sini6a/bratski-keyboard/keycaps/1x2.75 R2.stl

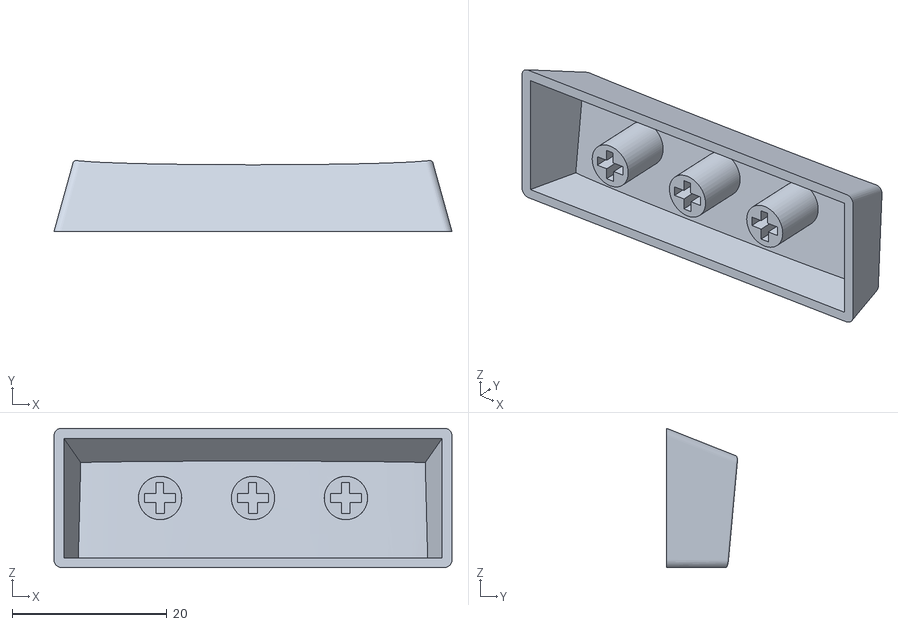
[picture p21: CAD file, 2024-02-13]
keycaps/1x2.75 R2.stl
51.4 x 9.14 x 18.0
