sini6a/bratski-keyboard/keycaps/1x2 R1.stl

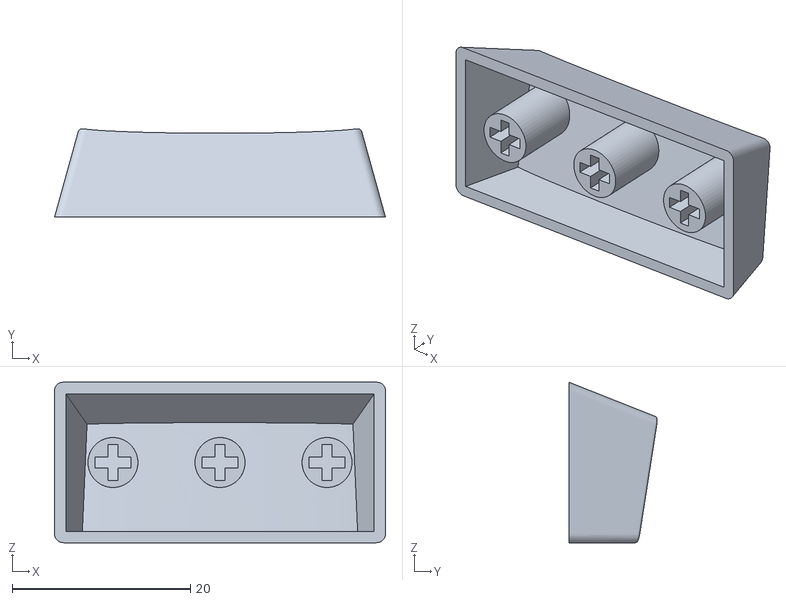
[picture p22: CAD file, 2024-02-13]
keycaps/1x2 R1.stl
37.1 x 9.88 x 18.0
