sini6a/bratski-keyboard/keycaps/1x1.25 R3.stl

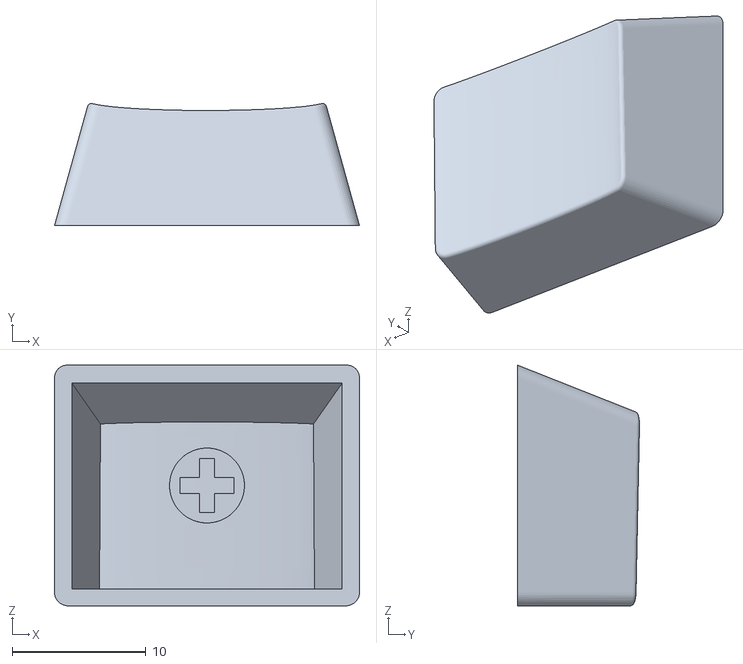
[picture p23: CAD file, 2024-02-13]
keycaps/1x1.25 R3.stl
22.8 x 9.12 x 18.0
