sini6a/bratski-keyboard/keycaps/1x6.25 R3.stl

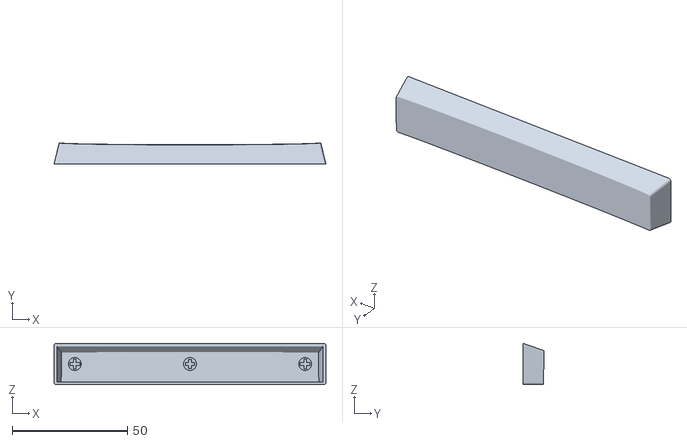
[picture p24: CAD file, 2024-02-13]
keycaps/1x6.25 R3.stl
118.1 x 9.20 x 18.0
