sini6a/bratski-keyboard/keycaps/1x1.5 R1.stl

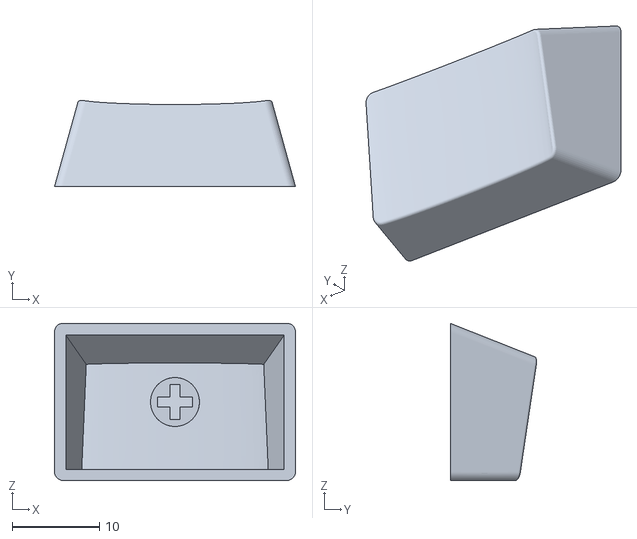
[picture p25: CAD file, 2024-02-13]
keycaps/1x1.5 R1.stl
27.6 x 9.86 x 18.0
