sini6a/bratski-keyboard/keycaps/1x1 R1.stl

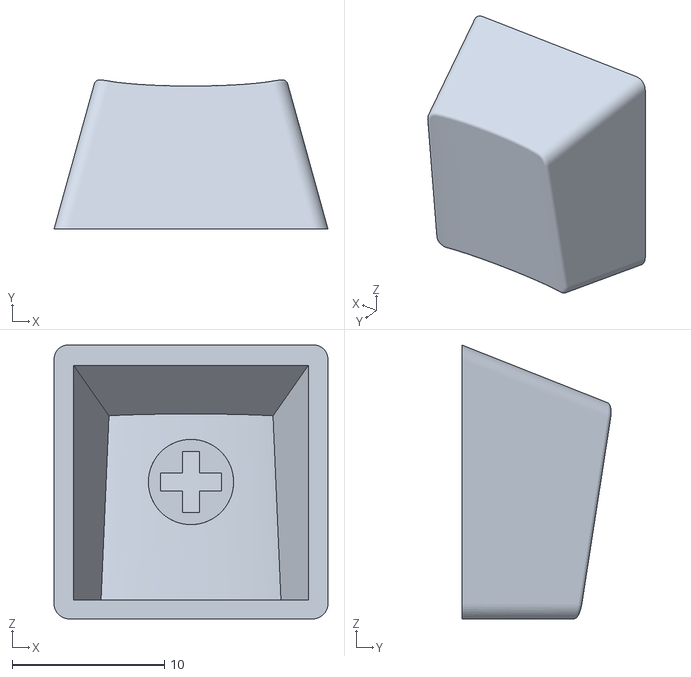
[picture p26: CAD file, 2024-02-13]
keycaps/1x1 R1.stl
18.0 x 9.80 x 18.0
