sini6a/bratski-keyboard/keycaps/1x1.75 R2.stl

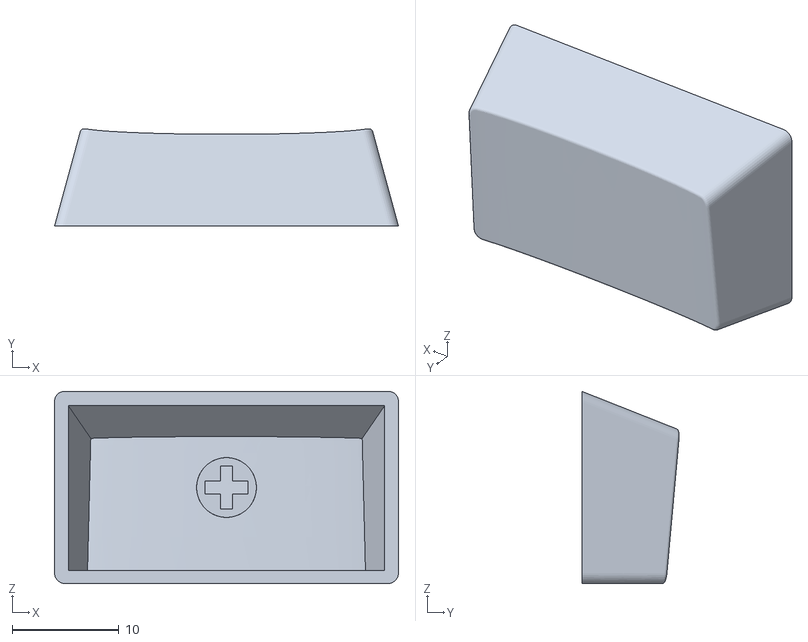
[picture p27: CAD file, 2024-02-13]
keycaps/1x1.75 R2.stl
32.2 x 9.10 x 18.0
