sini6a/bratski-keyboard/keycaps/1x6.25 R4.stl

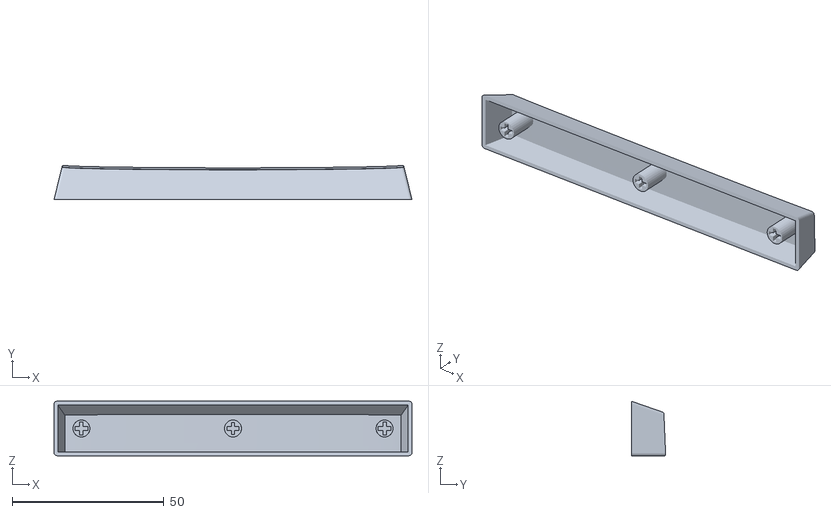
[picture p28: CAD file, 2024-02-13]
keycaps/1x6.25 R4.stl
118.1 x 11.3 x 18.0
