sini6a/bratski-keyboard/keycaps/1x1.75 R3.stl

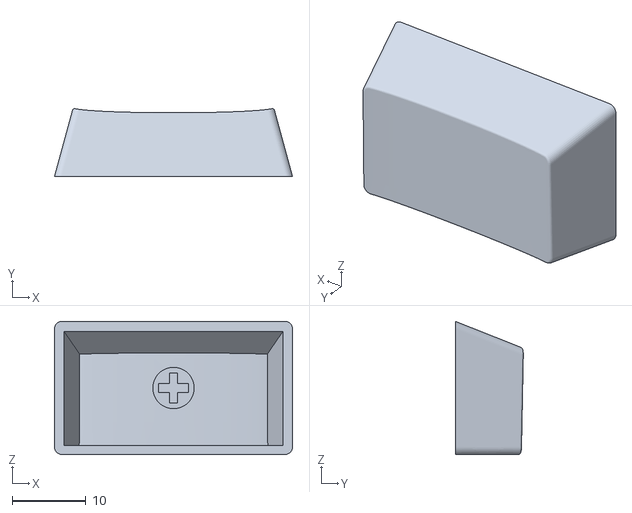
[picture p29: CAD file, 2024-02-13]
keycaps/1x1.75 R3.stl
32.2 x 9.15 x 18.0
