sini6a/bratski-keyboard/keycaps/1x2.25 R3.stl

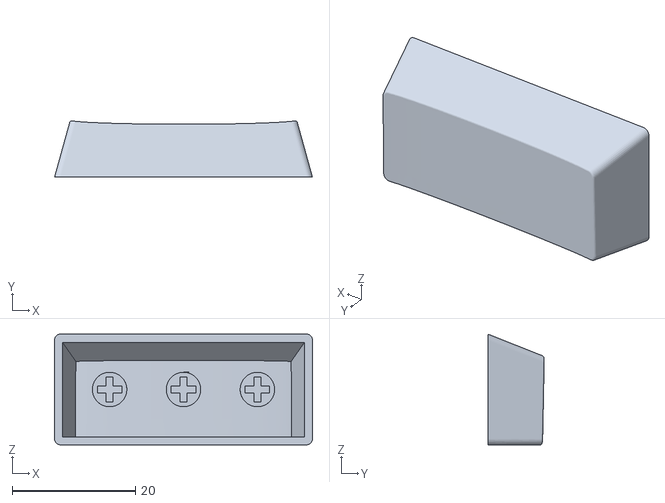
[picture p30: CAD file, 2024-02-13]
keycaps/1x2.25 R3.stl
41.9 x 9.16 x 18.0
