sini6a/bratski-keyboard/keycaps/1x2.25 R2.stl

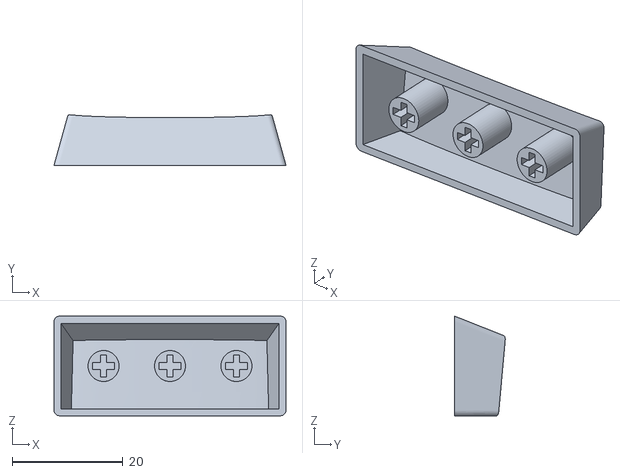
[picture p31: CAD file, 2024-02-13]
keycaps/1x2.25 R2.stl
41.9 x 9.12 x 18.0
