sini6a/bratski-keyboard/keycaps/1x2.25 R4.stl

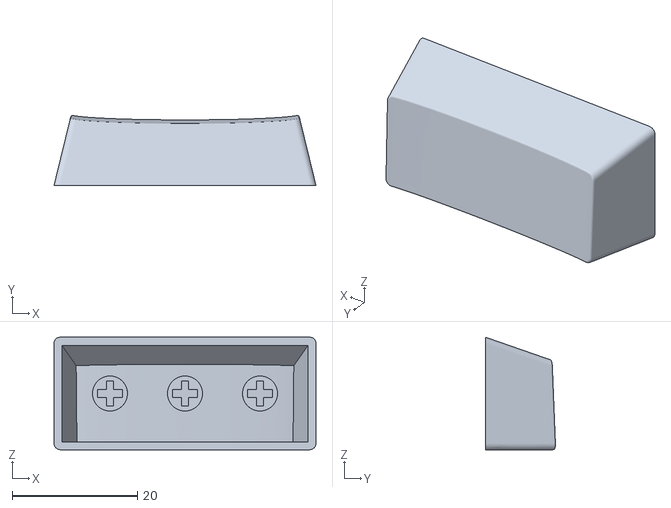
[picture p32: CAD file, 2024-02-13]
keycaps/1x2.25 R4.stl
41.9 x 11.2 x 18.0
