sini6a/bratski-keyboard/keycaps/1x2.5 R4.stl

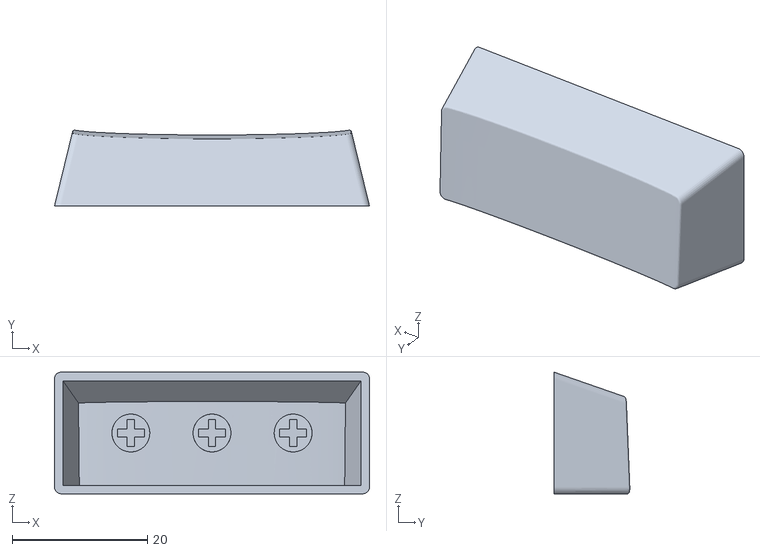
[picture p33: CAD file, 2024-02-13]
keycaps/1x2.5 R4.stl
46.6 x 11.2 x 18.0
