sini6a/bratski-keyboard/keycaps/1x1 R3.stl

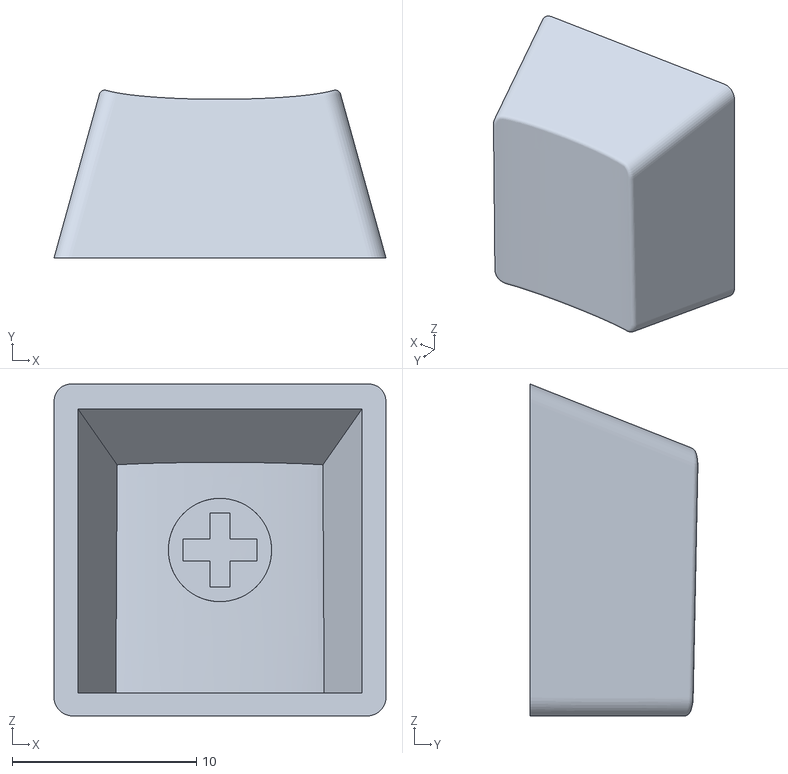
[picture p34: CAD file, 2024-02-13]
keycaps/1x1 R3.stl
18.0 x 9.09 x 18.0
