sini6a/bratski-keyboard/keycaps/1x1.75 R1.stl

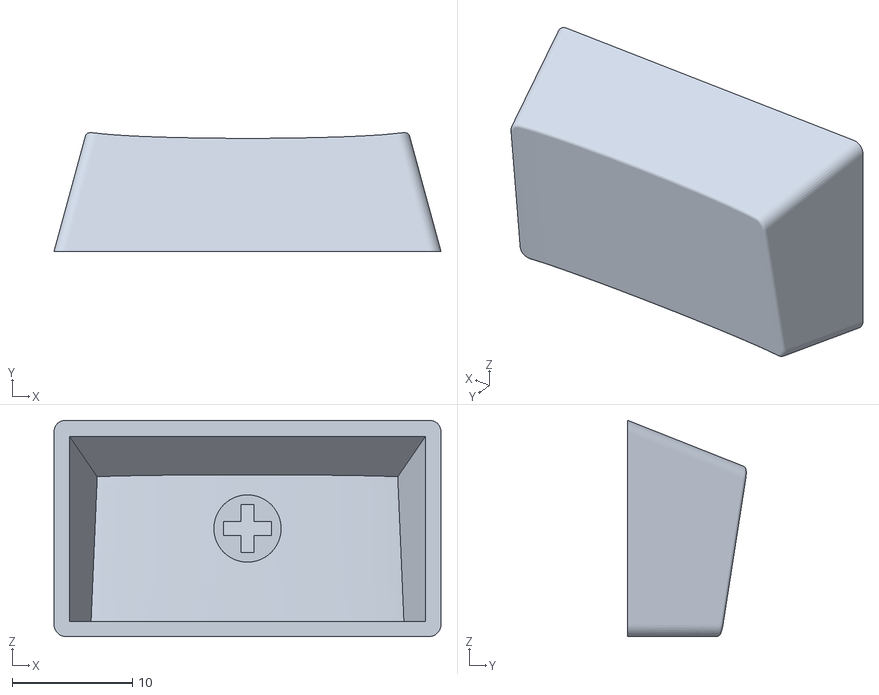
[picture p35: CAD file, 2024-02-13]
keycaps/1x1.75 R1.stl
32.2 x 9.87 x 18.0
