sini6a/bratski-keyboard/keycaps/1x2.5 R2.stl

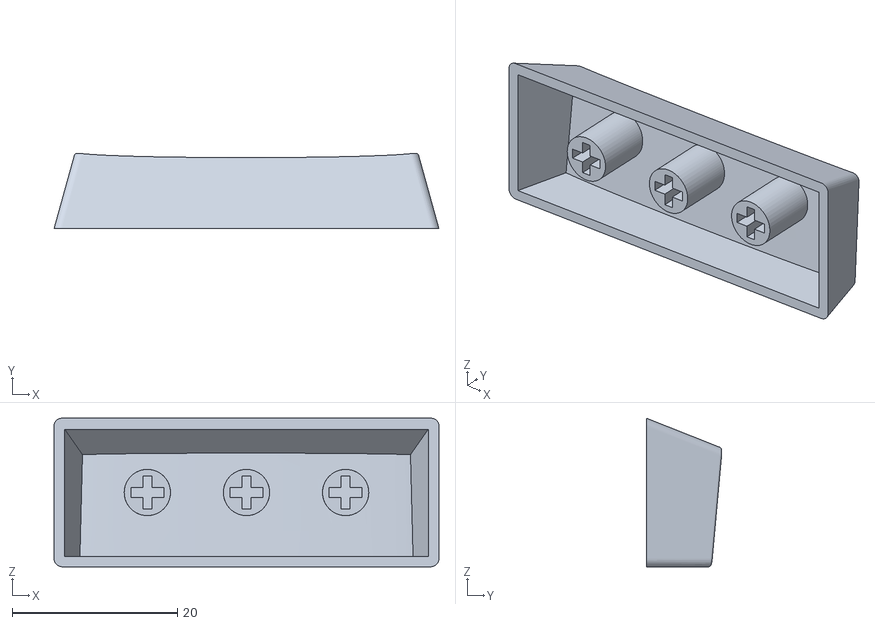
[picture p36: CAD file, 2024-02-13]
keycaps/1x2.5 R2.stl
46.6 x 9.13 x 18.0
