sini6a/bratski-keyboard/keycaps/1x1.5 R4.stl

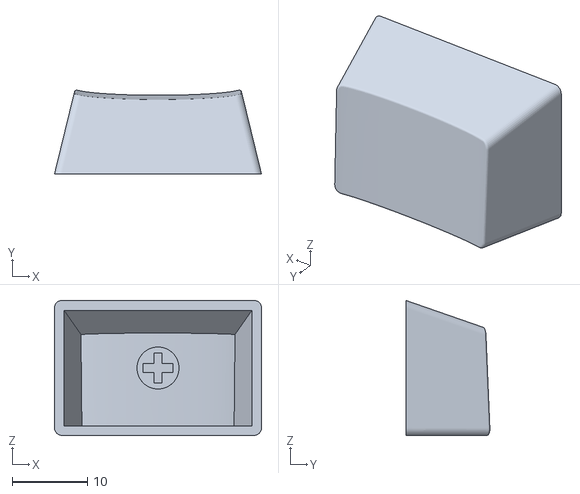
[picture p37: CAD file, 2024-02-13]
keycaps/1x1.5 R4.stl
27.6 x 11.2 x 18.0
