sini6a/bratski-keyboard/keycaps/1x1.75 R4.stl

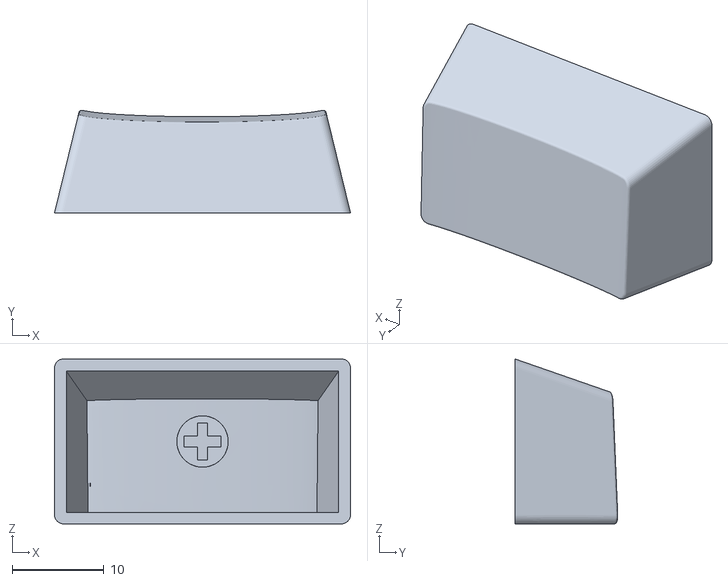
[picture p38: CAD file, 2024-02-13]
keycaps/1x1.75 R4.stl
32.3 x 11.2 x 18.0
