sini6a/bratski-keyboard/keycaps/1x2.5 R1.stl

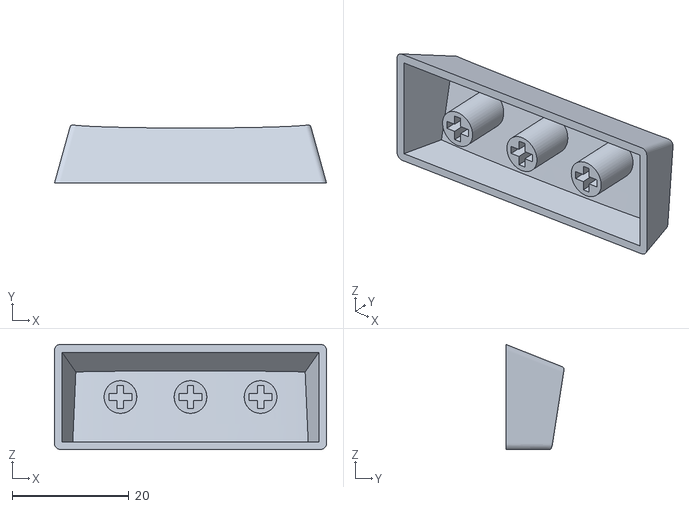
[picture p39: CAD file, 2024-02-13]
keycaps/1x2.5 R1.stl
46.6 x 9.90 x 18.0
