sini6a/bratski-keyboard/keycaps/1x6.25 R2.stl

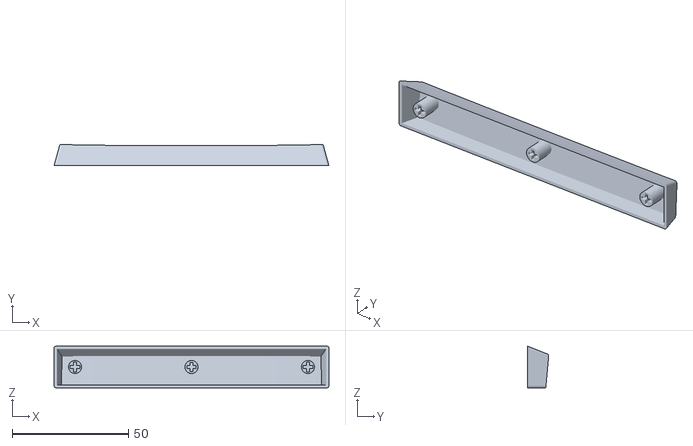
[picture p40: CAD file, 2024-02-13]
keycaps/1x6.25 R2.stl
118.1 x 9.18 x 18.0
