sini6a/bratski-keyboard/keycaps/1x6.25 R1.stl

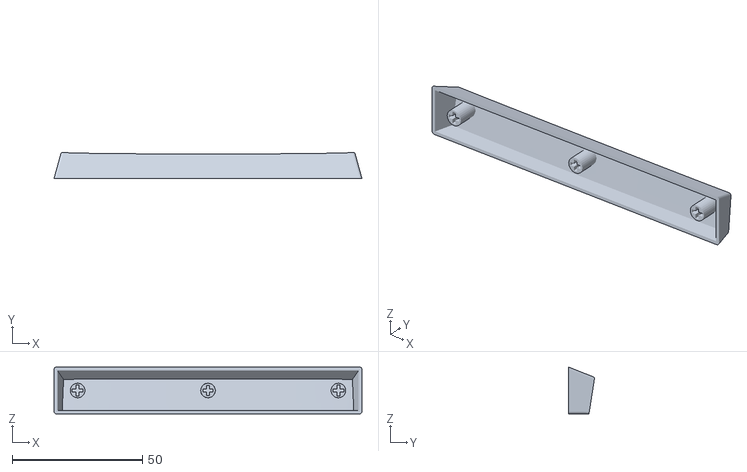
[picture p41: CAD file, 2024-02-13]
keycaps/1x6.25 R1.stl
118.1 x 9.96 x 18.0
