sini6a/bratski-keyboard/keycaps/1x2 R3.stl

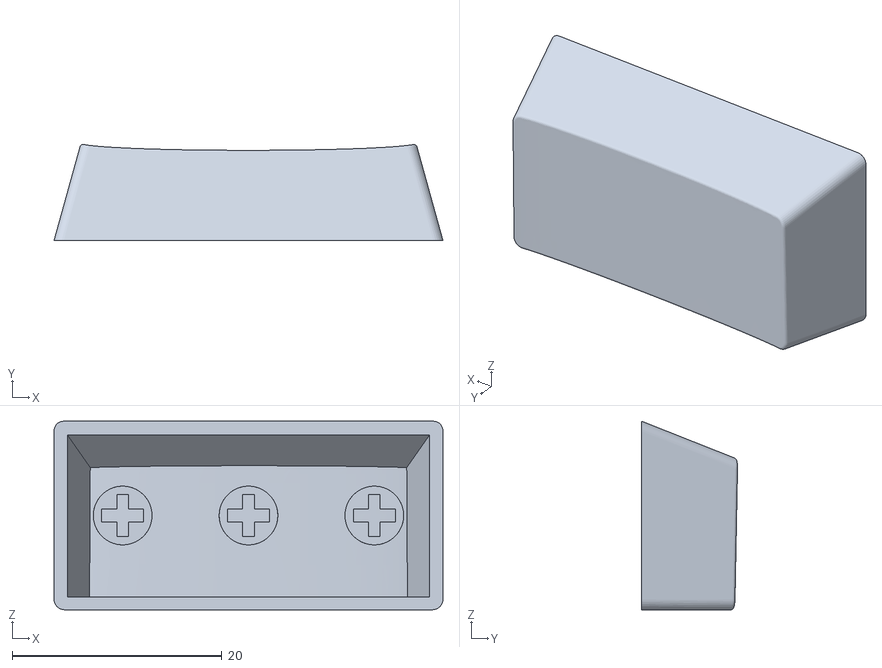
[picture p42: CAD file, 2024-02-13]
keycaps/1x2 R3.stl
37.1 x 9.17 x 18.0
