sini6a/bratski-keyboard/keycaps/1x2.75 R3.stl

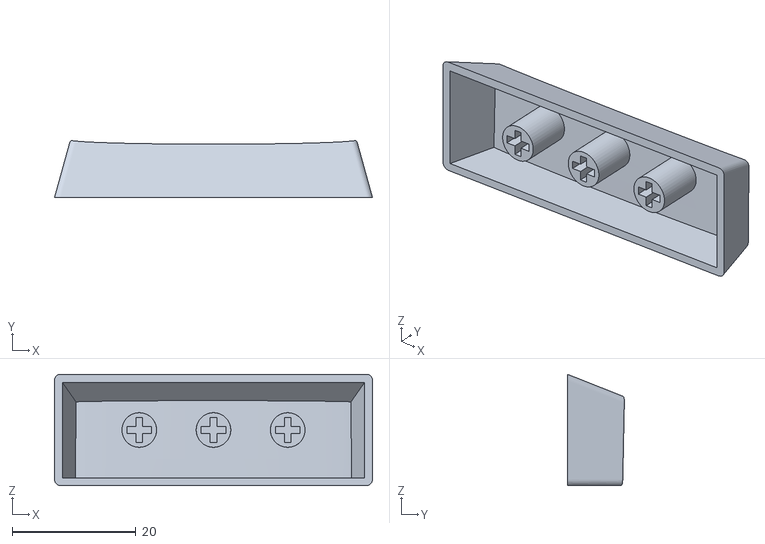
[picture p43: CAD file, 2024-02-13]
keycaps/1x2.75 R3.stl
51.4 x 9.18 x 18.0
